Scottapotamas/RX4/CAD/Other/232_0.jpg

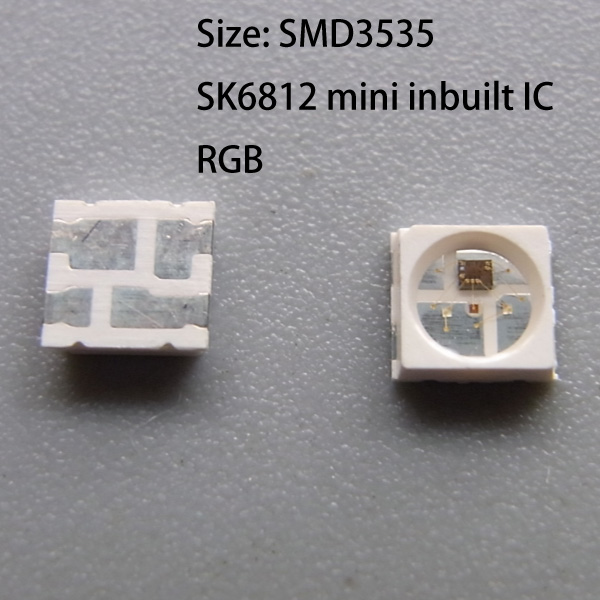
CAD/Other/232_0.jpg
