Scottapotamas/RX4/CAD/Enclosure Mockup/OLED 0.91in with PCB.SLDPRT

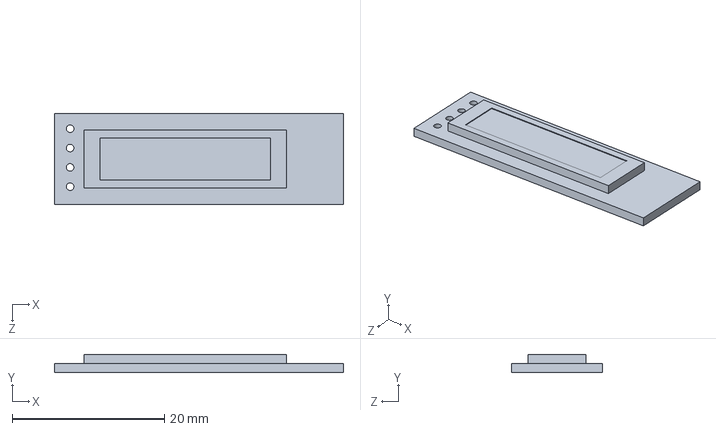
[picture p22: CAD file, 2017-02-19]
CAD/Enclosure Mockup/OLED 0.91in with PCB.SLDPRT
38.0 x 2.40 x 12.0 mm
