Scottapotamas/RX4/CAD/Enclosure Mockup/Lid.SLDPRT

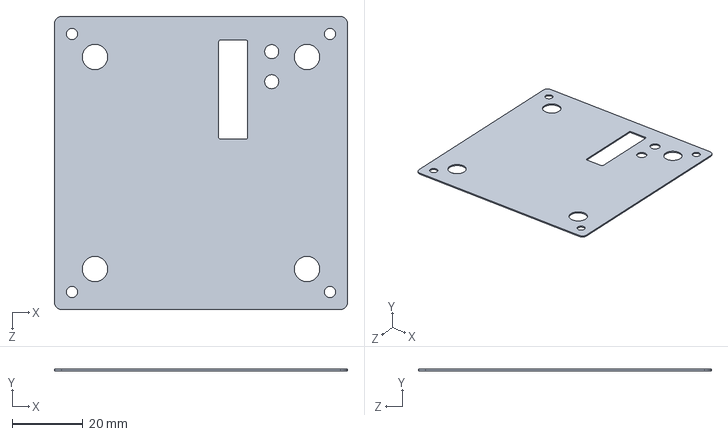
[picture p23: CAD file, 2017-02-19]
CAD/Enclosure Mockup/Lid.SLDPRT
82.9 x 0.5 x 82.9 mm
