Scottapotamas/RX4/CAD/Enclosure Mockup/Alu enclosure.SLDPRT

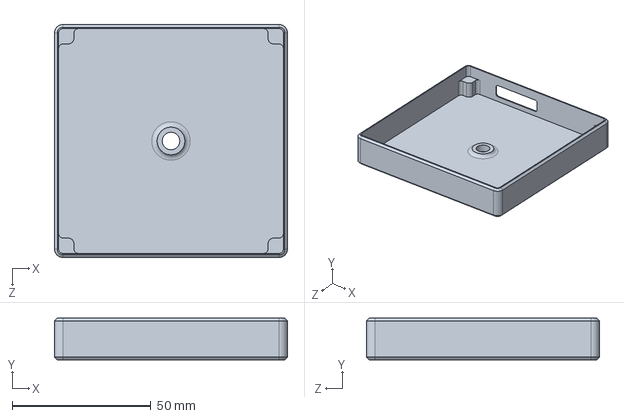
[picture p24: CAD file, 2017-02-19]
CAD/Enclosure Mockup/Alu enclosure.SLDPRT
84.0 x 15.0 x 84.0 mm
